A4091/A4092/Docs/A4092_REVC.png

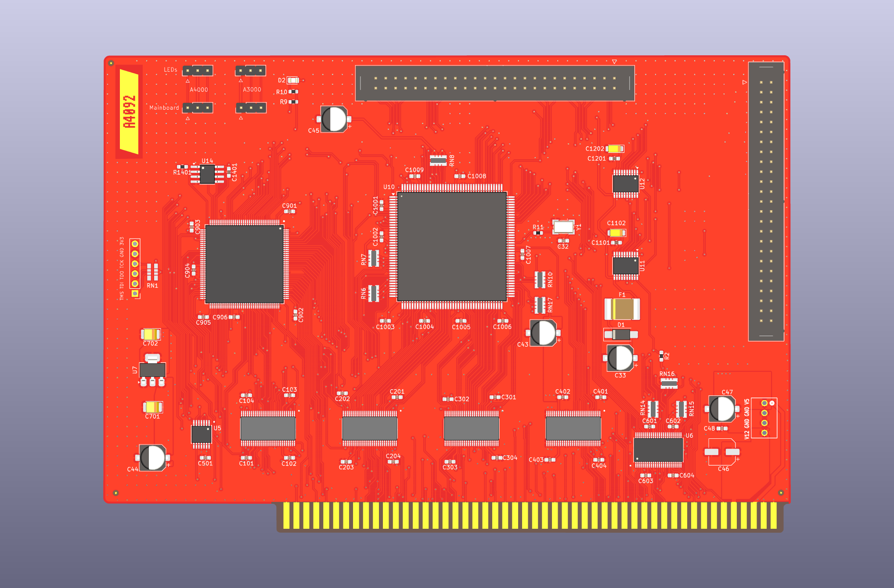
Docs/A4092_REVC.png
